loncardom/arkenswoop/images/exports/plates/left.png

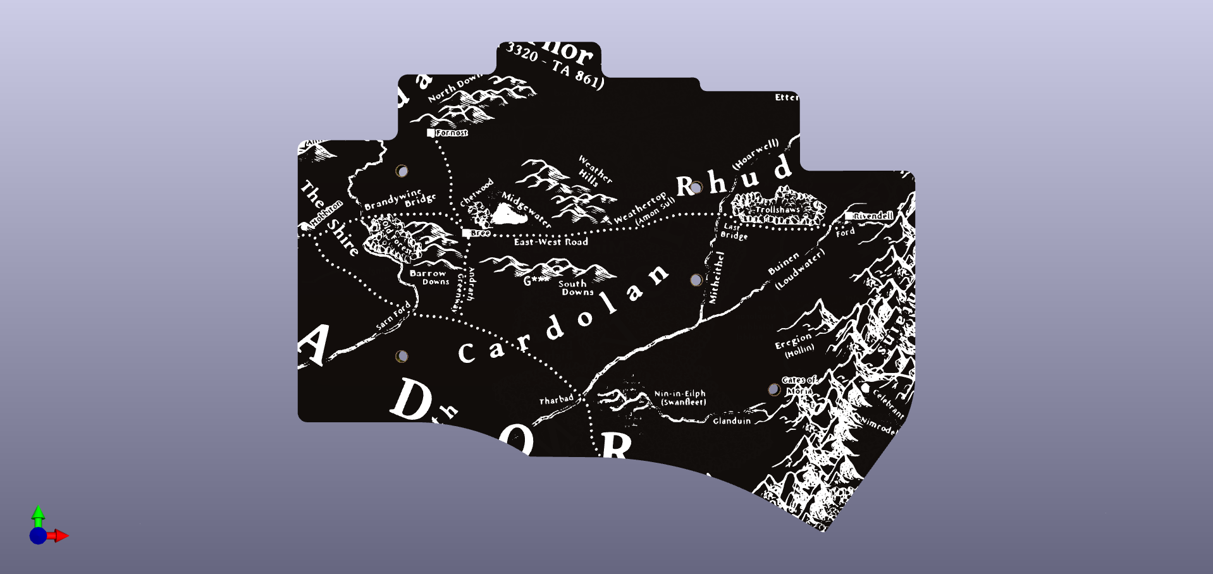
images/exports/plates/left.png
