loncardom/arkenswoop/images/exports/plates/right.png

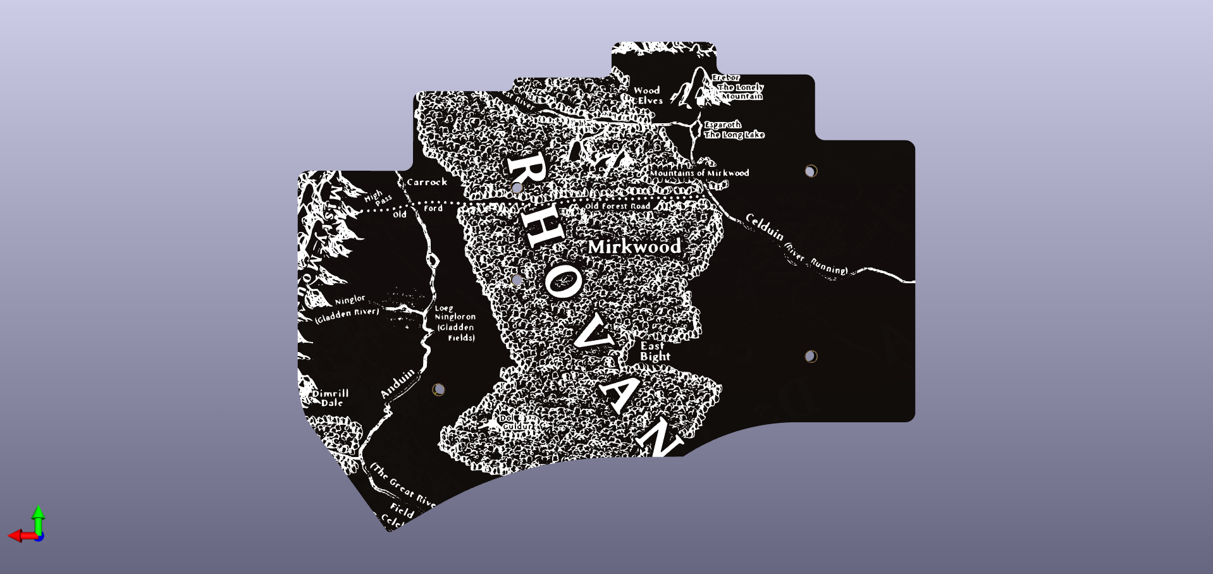
images/exports/plates/right.png
