loncardom/arkenswoop/images/build/00_naked_pcb.jpg

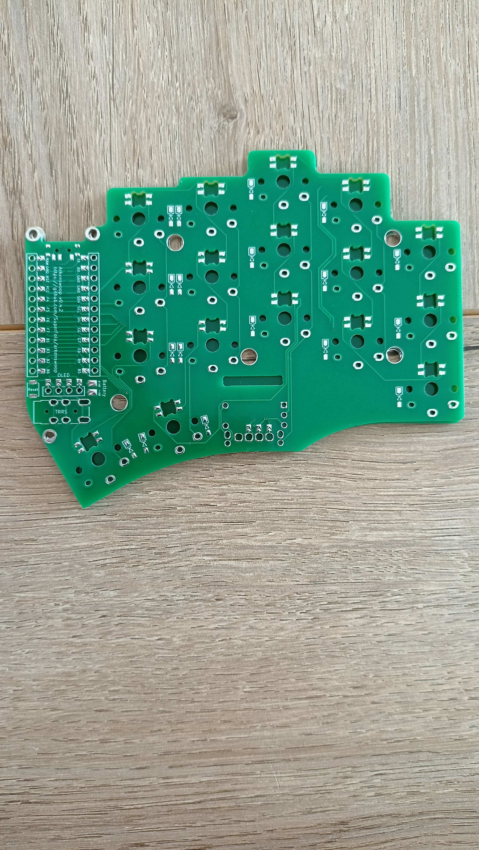
images/build/00_naked_pcb.jpg
