loncardom/arkenswoop/images/build/01_soldered_mcu_pads.jpg

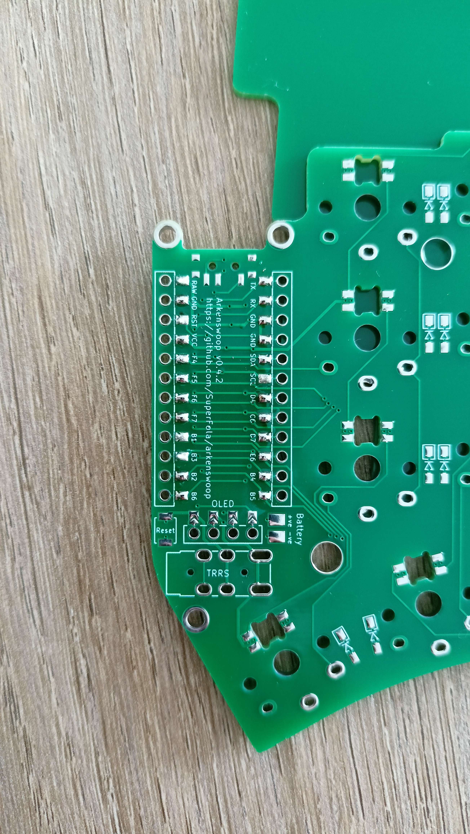
images/build/01_soldered_mcu_pads.jpg
