loncardom/arkenswoop/images/build/02_soldering_diodes.jpg

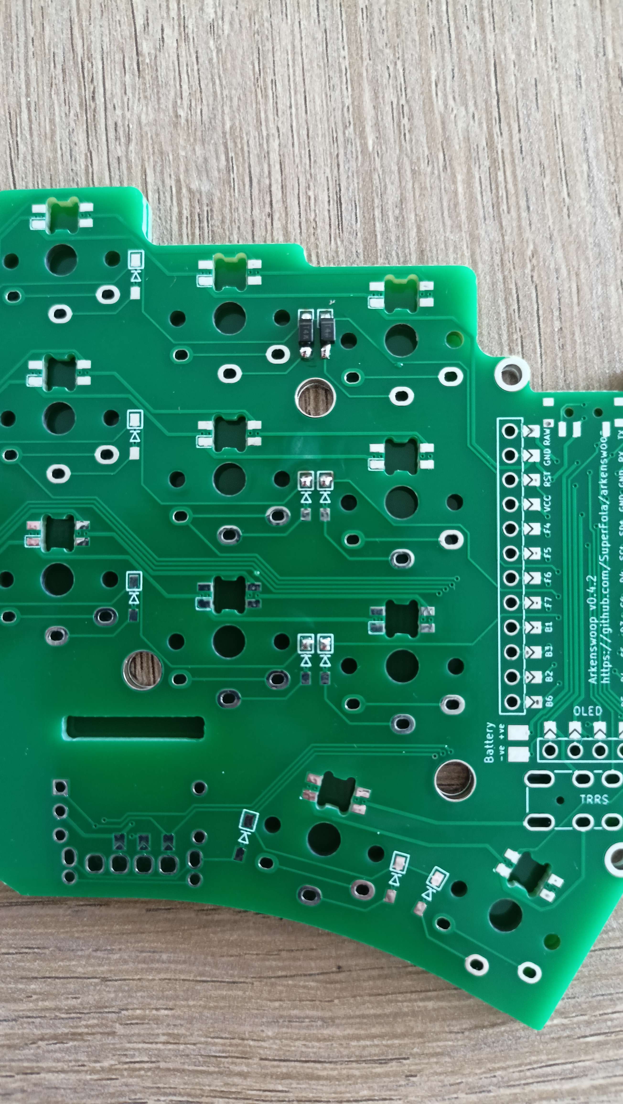
images/build/02_soldering_diodes.jpg
