loncardom/arkenswoop/images/build/03_more_diodes.jpg

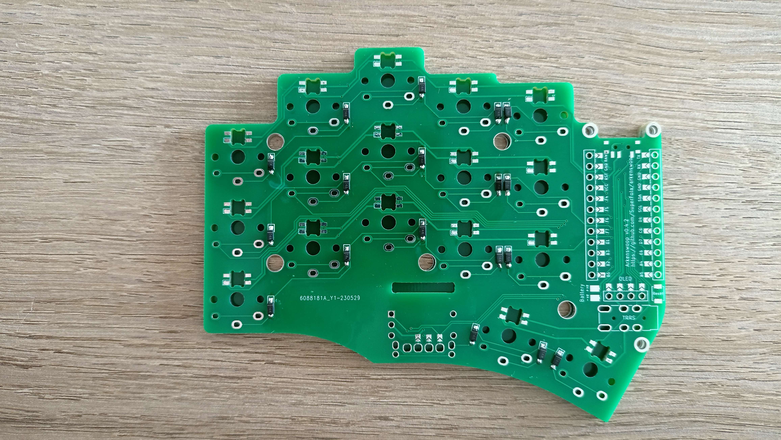
images/build/03_more_diodes.jpg
