loncardom/arkenswoop/images/build/06_mcu_sockets_and_jumper_pads.jpg

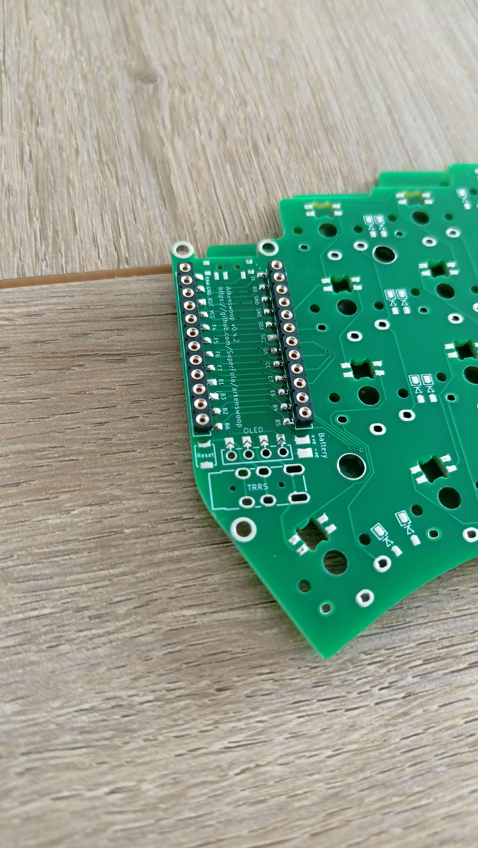
images/build/06_mcu_sockets_and_jumper_pads.jpg
