loncardom/arkenswoop/images/build/07_mcu_sockets_soldered.jpg

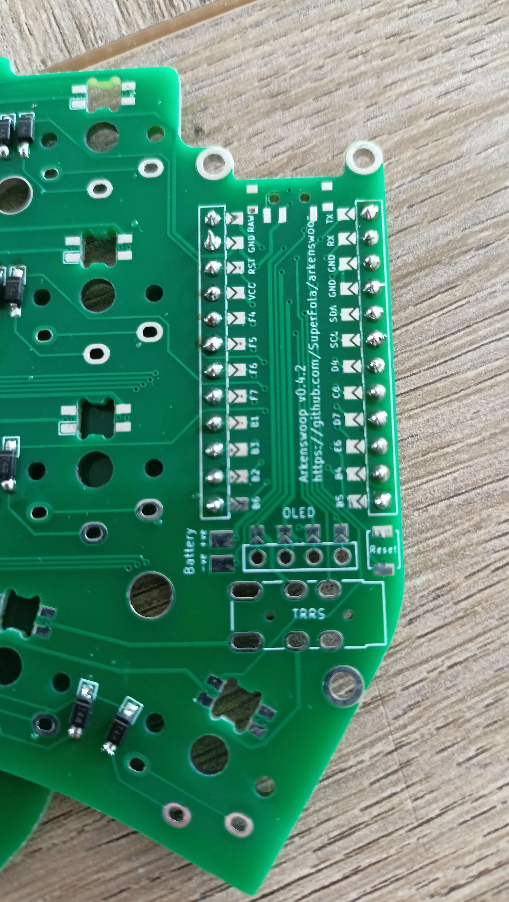
images/build/07_mcu_sockets_soldered.jpg
