loncardom/arkenswoop/images/build/08_putting_switches.jpg

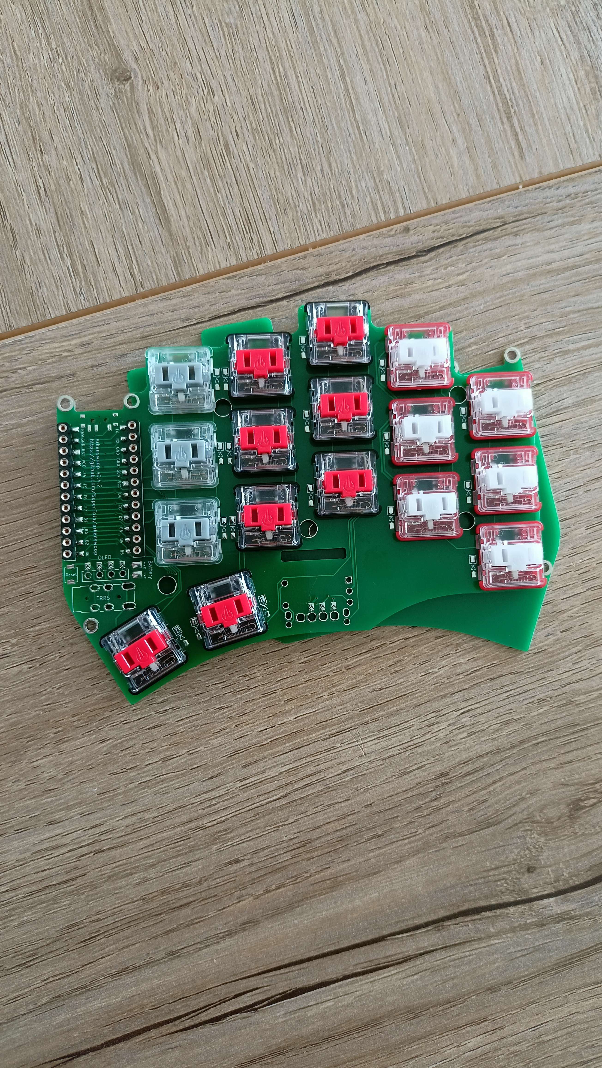
images/build/08_putting_switches.jpg
