loncardom/arkenswoop/images/build/09_switches_underneath_pcb.jpg

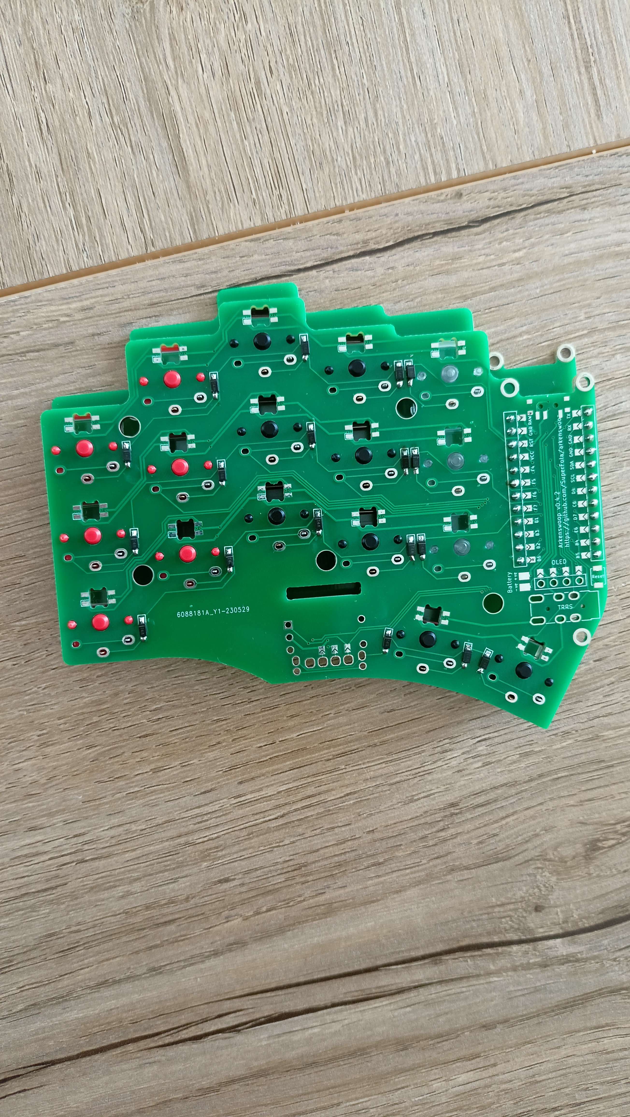
images/build/09_switches_underneath_pcb.jpg
