loncardom/arkenswoop/images/build/10_soldered_switches_underneath_pcb.jpg

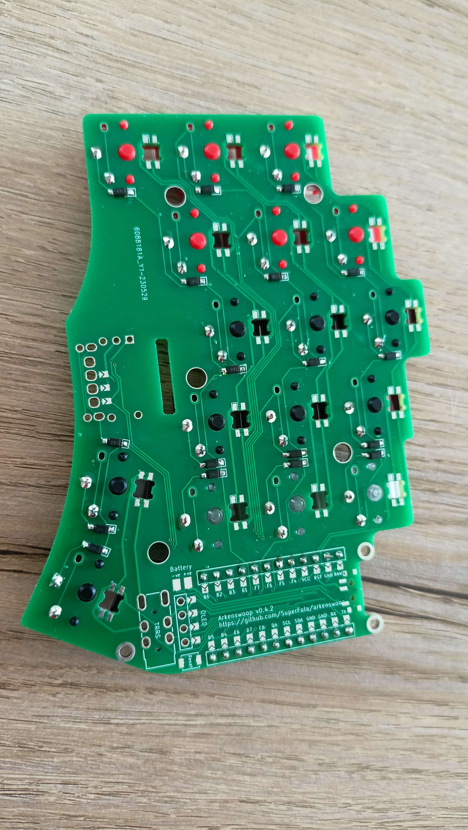
images/build/10_soldered_switches_underneath_pcb.jpg
