loncardom/arkenswoop/images/build/11_soldering_forgotten_trrs_jack.jpg

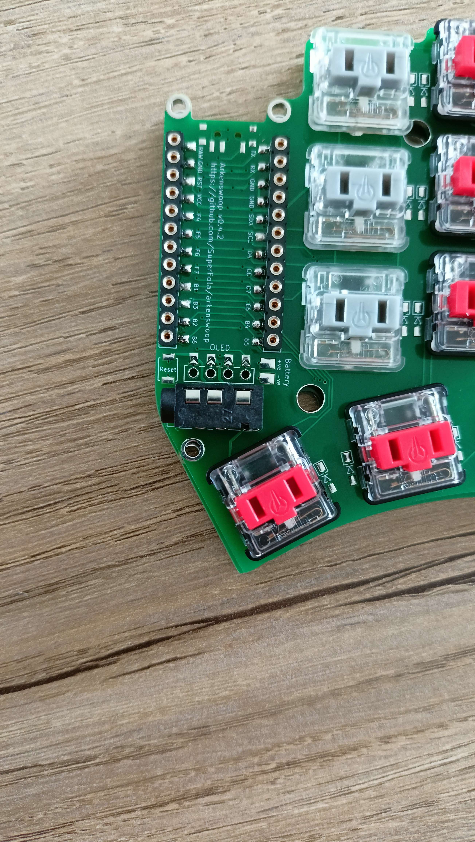
images/build/11_soldering_forgotten_trrs_jack.jpg
