loncardom/arkenswoop/images/build/14_complete_build_keycaps.jpg

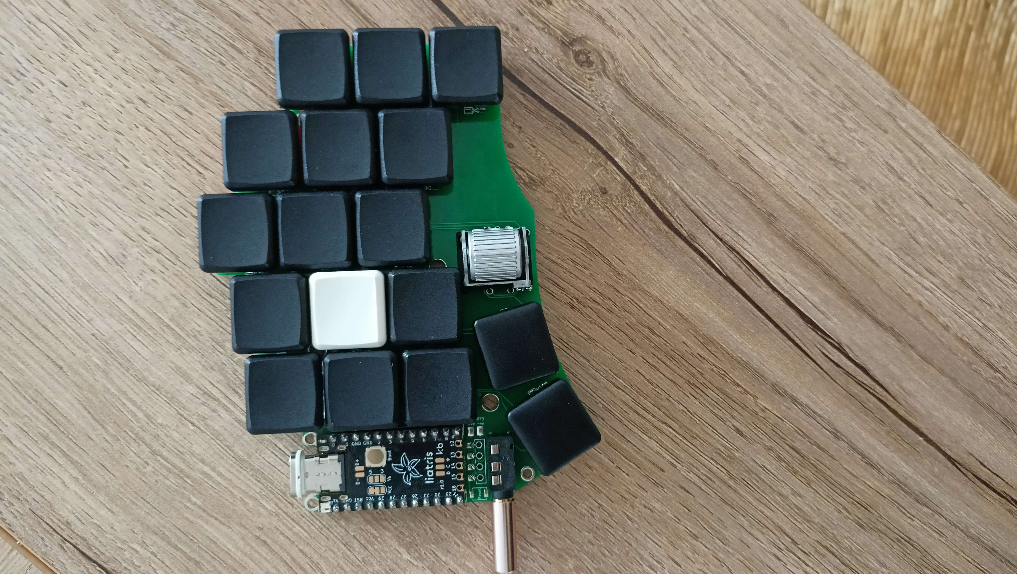
images/build/14_complete_build_keycaps.jpg
