loncardom/arkenswoop/images/build/right_half.jpg

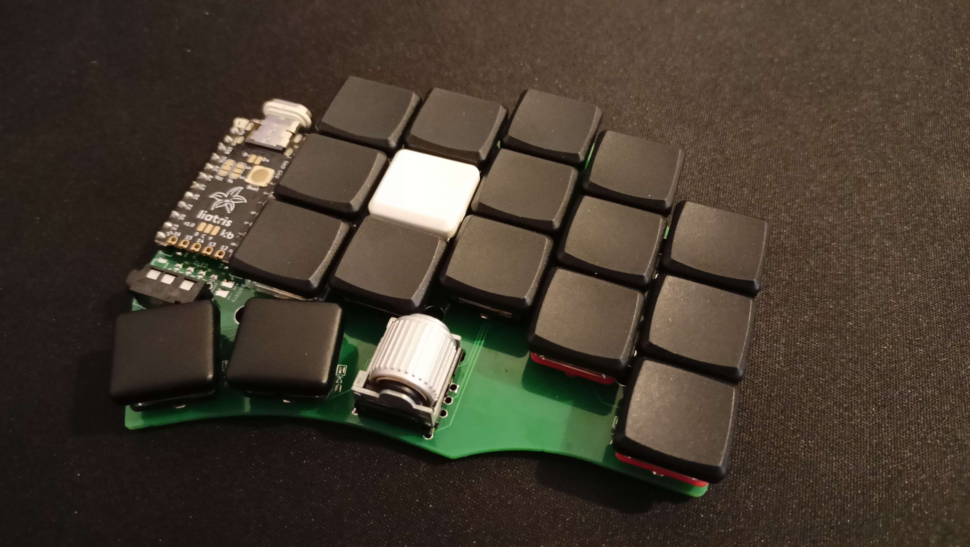
images/build/right_half.jpg
